sparkfun/SparkFun_RTK_Reference_Station/Rear_Panel/CORS_Rear_Panel.png

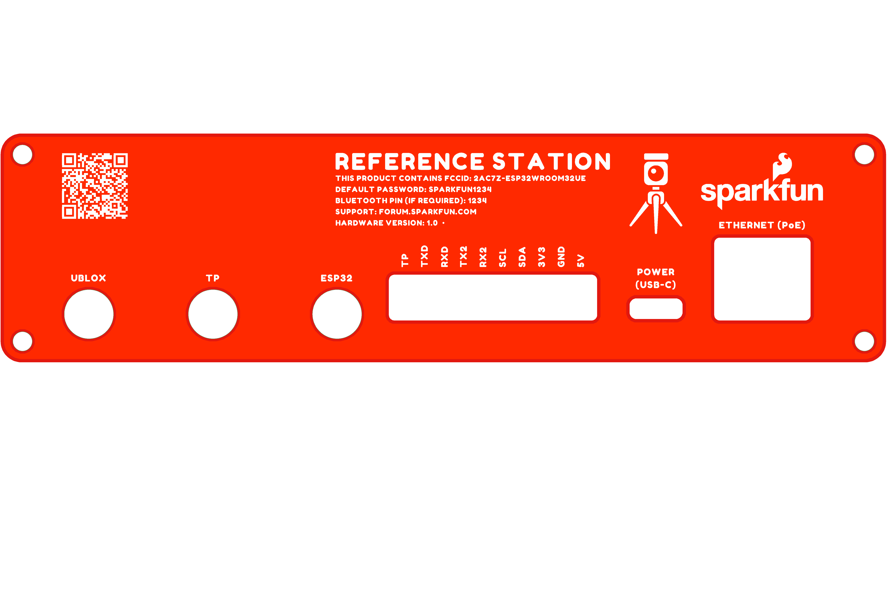
Rear_Panel/CORS_Rear_Panel.png
