sparkfun/SparkFun_RTK_Reference_Station/Reference_Station_Test_Sketches/microSD_SDIO/microSD_SDIO.ino

/*
  SparkFun GNSS Reference Station Test Sketch

  Based on: https://github.com/espressif/arduino-esp32/blob/master/libraries/SD_MMC/examples/SDMMC_Test/SDMMC_Test.ino

  License: MIT. Please see LICENSE.md for more details

  Pin Allocations:
  D0  : Boot + Boot Button
  D1  : Serial TX (CH340 RX)
  D2  : SDIO DAT0 - via 74HC4066 switch
  D3  : Serial RX (CH340 TX)
  D4  : SDIO DAT1
  D5  : GNSS Chip Select
  D12 : SDIO DAT2 - via 74HC4066 switch
  D13 : SDIO DAT3
  D14 : SDIO CLK
  D15 : SDIO CMD - via 74HC4066 switch
  D16 : Serial1 RXD
  D17 : Serial1 TXD
  D18 : SPI SCK
  D19 : SPI POCI
  D21 : I2C SDA
  D22 : I2C SCL
  D23 : SPI PICO
  D25 : GNSS Time Pulse
  D26 : STAT LED
  D27 : Ethernet Chip Select
  D32 : PWREN
  D33 : Ethernet Interrupt
  A34 : GNSS TX RDY
  A35 : Board Detect (1.1V)
*/

#include "FS.h"
#include "SD_MMC.h"

const int GNSS_CS = 5; // Chip select for the GNSS SPI interface
const int ETHERNET_CS = 27; // Chip select for the WizNet 5500
const int PWREN = 32; // 3V3_SW and SDIO Enable
const int SERIAL1_TX = 17;
const int SERIAL1_RX = 16;

void listDir(fs::FS &fs, const char * dirname, uint8_t levels){
    Serial.printf("Listing directory: %s\n", dirname);

    File root = fs.open(dirname);
    if(!root){
        Serial.println("Failed to open directory");
        return;
    }
    if(!root.isDirectory()){
        Serial.println("Not a directory");
        return;
    }

    File file = root.openNextFile();
    while(file){
        if(file.isDirectory()){
            Serial.print("  DIR : ");
            Serial.println(file.name());
            if(levels){
                listDir(fs, file.path(), levels -1);
            }
        } else {
            Serial.print("  FILE: ");
            Serial.print(file.name());
            Serial.print("  SIZE: ");
            Serial.println(file.size());
        }
        file = root.openNextFile();
    }
}

void createDir(fs::FS &fs, const char * path){
    Serial.printf("Creating Dir: %s\n", path);
    if(fs.mkdir(path)){
        Serial.println("Dir created");
    } else {
        Serial.println("mkdir failed");
    }
}

void removeDir(fs::FS &fs, const char * path){
    Serial.printf("Removing Dir: %s\n", path);
    if(fs.rmdir(path)){
        Serial.println("Dir removed");
    } else {
        Serial.println("rmdir failed");
    }
}

void readFile(fs::FS &fs, const char * path){
    Serial.printf("Reading file: %s\n", path);

    File file = fs.open(path);
    if(!file){
        Serial.println("Failed to open file for reading");
        return;
    }

    Serial.print("Read from file: ");
    while(file.available()){
        Serial.write(file.read());
    }
}

void writeFile(fs::FS &fs, const char * path, const char * message){
    Serial.printf("Writing file: %s\n", path);

    File file = fs.open(path, FILE_WRITE);
    if(!file){
        Serial.println("Failed to open file for writing");
        return;
    }
    if(file.print(message)){
        Serial.println("File written");
    } else {
        Serial.println("Write failed");
    }
}

void appendFile(fs::FS &fs, const char * path, const char * message){
    Serial.printf("Appending to file: %s\n", path);

    File file = fs.open(path, FILE_APPEND);
    if(!file){
        Serial.println("Failed to open file for appending");
        return;
    }
    if(file.print(message)){
        Serial.println("Message appended");
    } else {
        Serial.println("Append failed");
    }
}

void renameFile(fs::FS &fs, const char * path1, const char * path2){
    Serial.printf("Renaming file %s to %s\n", path1, path2);
    if (fs.rename(path1, path2)) {
        Serial.println("File renamed");
    } else {
        Serial.println("Rename failed");
    }
}

void deleteFile(fs::FS &fs, const char * path){
    Serial.printf("Deleting file: %s\n", path);
    if(fs.remove(path)){
        Serial.println("File deleted");
    } else {
        Serial.println("Delete failed");
    }
}

void testFileIO(fs::FS &fs, const char * path){
    File file = fs.open(path);
    static uint8_t buf[512];
    size_t len = 0;
    uint32_t start = millis();
    uint32_t end = start;
    if(file){
        len = file.size();
        size_t flen = len;
        start = millis();
        while(len){
            size_t toRead = len;
            if(toRead > 512){
                toRead = 512;
            }
            file.read(buf, toRead);
            len -= toRead;
        }
        end = millis() - start;
        Serial.printf("%u bytes read for %u ms\n", flen, end);
        file.close();
    } else {
        Serial.println("Failed to open file for reading");
    }


    file = fs.open(path, FILE_WRITE);
    if(!file){
        Serial.println("Failed to open file for writing");
        return;
    }

    size_t i;
    start = millis();
    for(i=0; i<2048; i++){
        file.write(buf, 512);
    }
    end = millis() - start;
    Serial.printf("%u bytes written for %u ms\n", 2048 * 512, end);
    file.close();
}

void setup()
{
  pinMode(GNSS_CS, OUTPUT);
  digitalWrite(GNSS_CS, HIGH);
  pinMode(ETHERNET_CS, OUTPUT);
  digitalWrite(ETHERNET_CS, HIGH);
  pinMode(PWREN, OUTPUT);
  digitalWrite(PWREN, HIGH);

  delay(1000);

  Serial.begin(115200);
  Serial.println("SparkFun Reference Station - Test Sketch");

  if(!SD_MMC.begin()){
      Serial.println("Card Mount Failed");
      return;
  }
  
  uint8_t cardType = SD_MMC.cardType();

  if(cardType == CARD_NONE){
      Serial.println("No SD_MMC card attached");
      return;
  }

  Serial.print("SD_MMC Card Type: ");
  if(cardType == CARD_MMC){
      Serial.println("MMC");
  } else if(cardType == CARD_SD){
      Serial.println("SDSC");
  } else if(cardType == CARD_SDHC){
      Serial.println("SDHC");
  } else {
      Serial.println("UNKNOWN");
  }

  uint64_t cardSize = SD_MMC.cardSize() / (1024 * 1024);
  Serial.printf("SD_MMC Card Size: %lluMB\n", cardSize);

  listDir(SD_MMC, "/", 0);
  createDir(SD_MMC, "/mydir");
  listDir(SD_MMC, "/", 0);
  removeDir(SD_MMC, "/mydir");
  listDir(SD_MMC, "/", 2);
  writeFile(SD_MMC, "/hello.txt", "Hello ");
  appendFile(SD_MMC, "/hello.txt", "World!\n");
  readFile(SD_MMC, "/hello.txt");
  deleteFile(SD_MMC, "/foo.txt");
  renameFile(SD_MMC, "/hello.txt", "/foo.txt");
  readFile(SD_MMC, "/foo.txt");
  testFileIO(SD_MMC, "/test.txt");
  Serial.printf("Total space: %lluMB\n", SD_MMC.totalBytes() / (1024 * 1024));
  Serial.printf("Used space: %lluMB\n", SD_MMC.usedBytes() / (1024 * 1024));
}

void loop()
{
  // Nothing to do here...
}
