sparkfun/SparkFun_RTK_Reference_Station/Reference_Station_Test_Sketches/ATECC608_Crypto/ATECC608_Crypto.ino

/*
  SparkFun GNSS Reference Station Test Sketch

  License: MIT. Please see LICENSE.md for more details

  Pin Allocations:
  D0  : Boot + Boot Button
  D1  : Serial TX (CH340 RX)
  D2  : SDIO DAT0 - via 74HC4066 switch
  D3  : Serial RX (CH340 TX)
  D4  : SDIO DAT1
  D5  : GNSS Chip Select
  D12 : SDIO DAT2 - via 74HC4066 switch
  D13 : SDIO DAT3
  D14 : SDIO CLK
  D15 : SDIO CMD - via 74HC4066 switch
  D16 : Serial1 RXD
  D17 : Serial1 TXD
  D18 : SPI SCK
  D19 : SPI POCI
  D21 : I2C SDA
  D22 : I2C SCL
  D23 : SPI PICO
  D25 : GNSS Time Pulse
  D26 : STAT LED
  D27 : Ethernet Chip Select
  D32 : PWREN
  D33 : Ethernet Interrupt
  A34 : GNSS TX RDY
  A35 : Board Detect (1.1V)
*/

#include <Wire.h>

#include <SparkFun_ATECCX08a_Arduino_Library.h> //Click here to get the library: http://librarymanager/All#SparkFun_ATECCX08a

ATECCX08A atecc;

const int GNSS_CS = 5; // Chip select for the GNSS SPI interface
const int ETHERNET_CS = 27; // Chip select for the WizNet 5500
const int PWREN = 32; // 3V3_SW and SDIO Enable
const int STAT_LED = 26;
const int GNSS_INT = 25;

void setup()
{
  pinMode(GNSS_CS, OUTPUT);
  digitalWrite(GNSS_CS, HIGH);
  pinMode(ETHERNET_CS, OUTPUT);
  digitalWrite(ETHERNET_CS, HIGH);
  pinMode(PWREN, OUTPUT);
  digitalWrite(PWREN, HIGH);

  pinMode(STAT_LED, OUTPUT);

  delay(1000);

  Serial.begin(115200);
  Serial.println("SparkFun Reference Station - Test Sketch");

  Wire.begin();

  if (atecc.begin() == true)
  {
    Serial.println("Successful wakeUp(). I2C connections are good.");
  }
  else
  {
    Serial.println("Device not found. Check wiring.");
    while (1); // stall out forever
  }

  printInfo(); // see function below for library calls and data handling
}

void loop()
{
  // Nothing to do here
}

void printInfo()
{
  // Read all 128 bytes of Configuration Zone
  // These will be stored in an array within the instance named: atecc.configZone[128]
  atecc.readConfigZone(false); // Debug argument false (OFF)

  // Print useful information from configuration zone data
  Serial.println();

  Serial.print("Serial Number: \t");
  for (int i = 0 ; i < 9 ; i++)
  {
    if ((atecc.serialNumber[i] >> 4) == 0) Serial.print("0"); // print preceeding high nibble if it's zero
    Serial.print(atecc.serialNumber[i], HEX);
  }
  Serial.println();

  Serial.print("Rev Number: \t");
  for (int i = 0 ; i < 4 ; i++)
  {
    if ((atecc.revisionNumber[i] >> 4) == 0) Serial.print("0"); // print preceeding high nibble if it's zero
    Serial.print(atecc.revisionNumber[i], HEX);
  }
  Serial.println();

  Serial.print("Config Zone: \t");
  if (atecc.configLockStatus) Serial.println("Locked");
  else Serial.println("NOT Locked");

  Serial.print("Data/OTP Zone: \t");
  if (atecc.dataOTPLockStatus) Serial.println("Locked");
  else Serial.println("NOT Locked");

  Serial.print("Data Slot 0: \t");
  if (atecc.slot0LockStatus) Serial.println("Locked");
  else Serial.println("NOT Locked");

  Serial.println();

  // if everything is locked up, then configuration is complete, so let's print the public key
  if (atecc.configLockStatus && atecc.dataOTPLockStatus && atecc.slot0LockStatus) 
  {
    if(atecc.generatePublicKey() == false)
    {
      Serial.println("Failure to generate This device's Public Key");
      Serial.println();
    }
  }
}
